PeterMunirAzmy/Automated-Production-line/Mechatronics System Desigen/RobotArm_mechanical_design/files/GearRotate_-0.10mmTolerance.stl

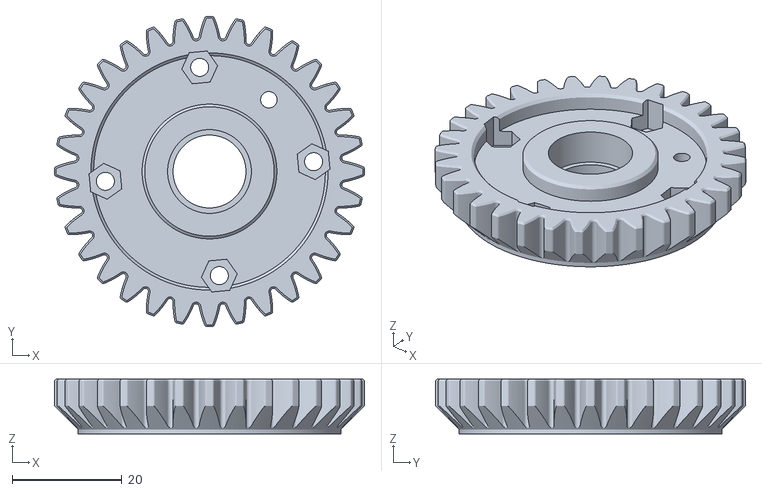
[picture p67: CAD file, 2024-07-03]
Mechatronics System Desigen/RobotArm_mechanical_design/files/GearRotate_-0.10mmTolerance.stl
56.6 x 56.6 x 10.0
