PeterMunirAzmy/Automated-Production-line/Mechatronics System Desigen/Feeding_mechanical_design/feeding_stepper_stand.stp

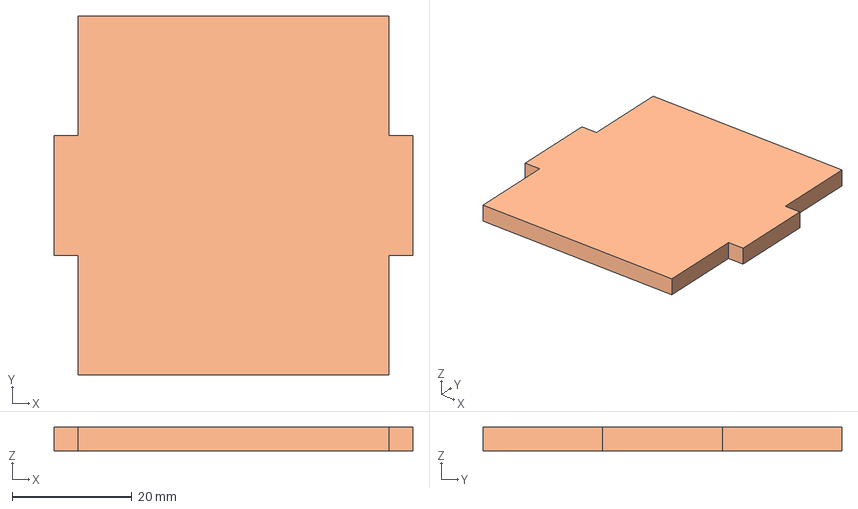
[picture p68: CAD file, 2024-07-03]
Mechatronics System Desigen/Feeding_mechanical_design/feeding_stepper_stand.stp
60.0 x 60.0 x 4.00 mm
