PeterMunirAzmy/Automated-Production-line/Mechatronics System Desigen/Robot_Arm_simulation_on_Matlab/ForwardKinematics/base_w_hole_ipt_7cfa0195.STEP

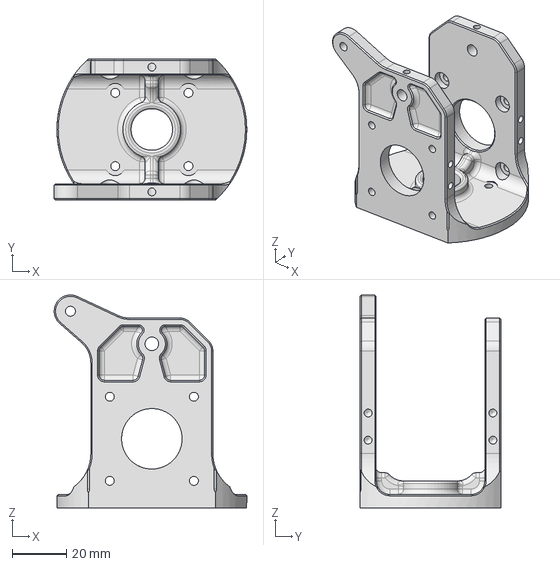
[picture p69: CAD file, 2024-07-03]
Mechatronics System Desigen/Robot_Arm_simulation_on_Matlab/ForwardKinematics/base_w_hole_ipt_7cfa0195.STEP
71.0 x 52.0 x 78.5 mm
