PeterMunirAzmy/Automated-Production-line/Mechatronics System Desigen/Robot_Arm_simulation_on_Matlab/trajectory/GearBig_0.20mmTolerance_ipt_e1a5b1e9.STEP

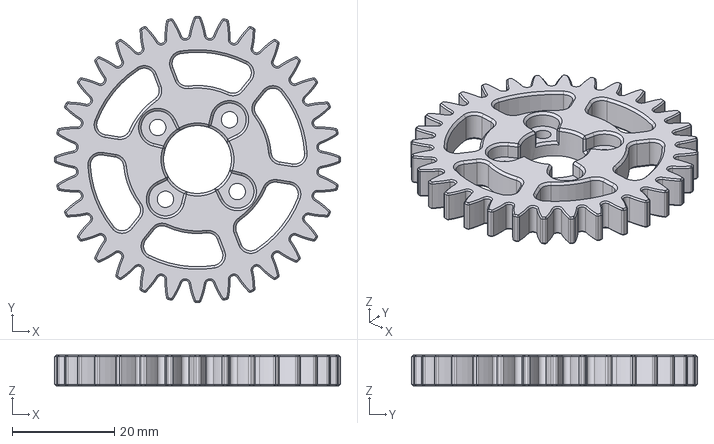
[picture p70: CAD file, 2024-07-03]
Mechatronics System Desigen/Robot_Arm_simulation_on_Matlab/trajectory/GearBig_0.20mmTolerance_ipt_e1a5b1e9.STEP
56.0 x 56.0 x 6.00 mm
