PeterMunirAzmy/Automated-Production-line/Mechatronics System Desigen/Feeding_mechanical_design/feeding_rotating_plate.stp

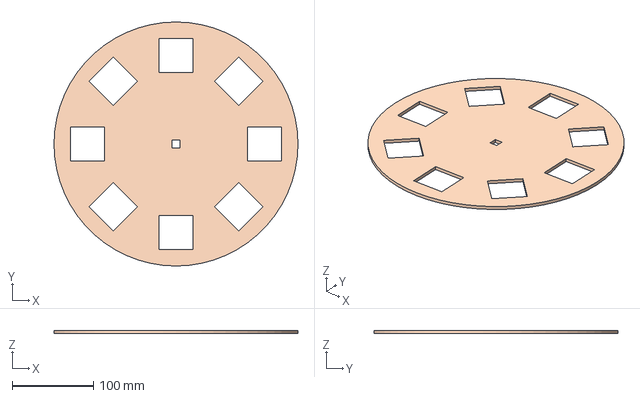
[picture p71: CAD file, 2024-07-03]
Mechatronics System Desigen/Feeding_mechanical_design/feeding_rotating_plate.stp
300.0 x 300.0 x 4.00 mm
