PeterMunirAzmy/Automated-Production-line/Mechatronics System Desigen/RobotArm_mechanical_design/files/gripperBase.stl

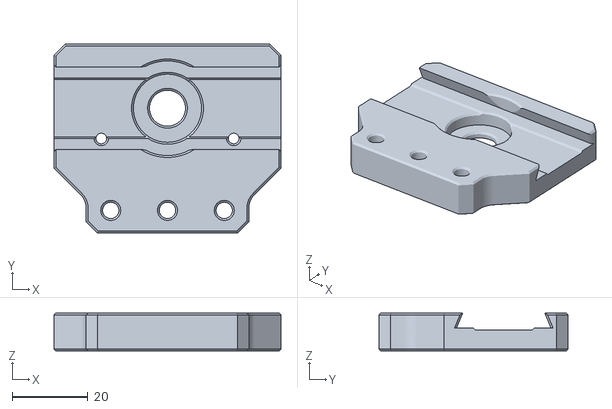
[picture p72: CAD file, 2024-07-03]
Mechatronics System Desigen/RobotArm_mechanical_design/files/gripperBase.stl
60.0 x 50.0 x 10.0
