PeterMunirAzmy/Automated-Production-line/Mechatronics System Desigen/Feeding_mechanical_design/stepper.stp

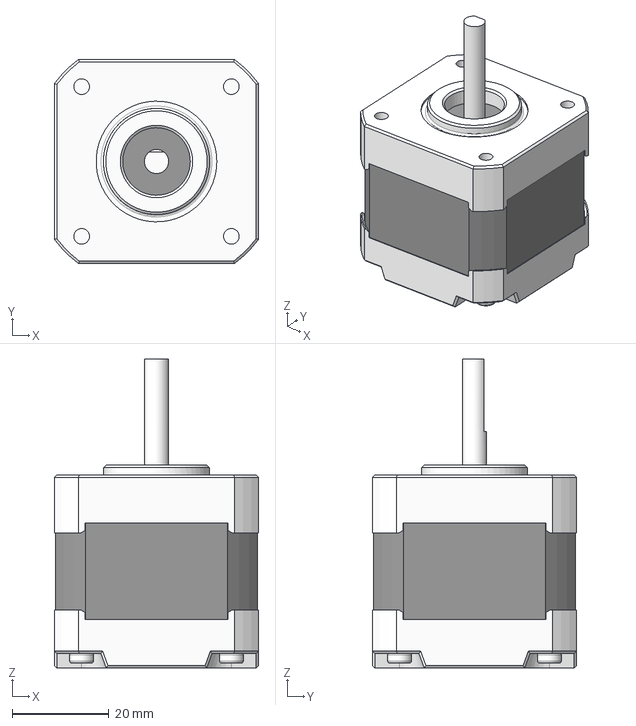
[picture p73: CAD file, 2024-07-03]
Mechatronics System Desigen/Feeding_mechanical_design/stepper.stp
42.3 x 42.3 x 64.0 mm
