PeterMunirAzmy/Automated-Production-line/Mechatronics System Desigen/Feeding_mechanical_design/feeding_stepper_side.stp

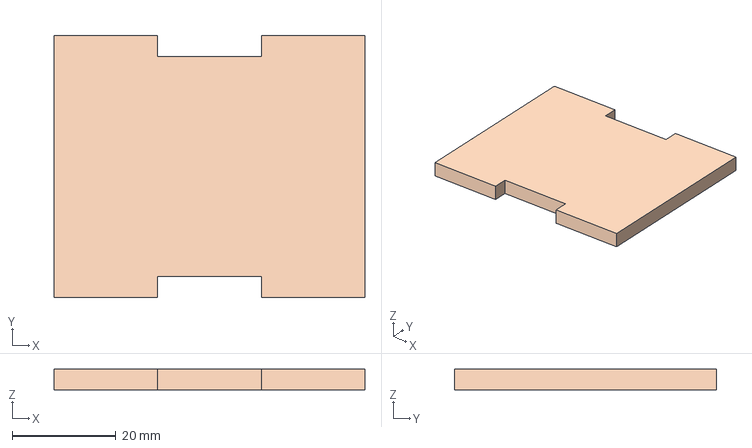
[picture p74: CAD file, 2024-07-03]
Mechatronics System Desigen/Feeding_mechanical_design/feeding_stepper_side.stp
60.0 x 50.5 x 4.00 mm
