PeterMunirAzmy/Automated-Production-line/Mechatronics System Desigen/RobotArm_mechanical_design/files/pleuel_bend.stl

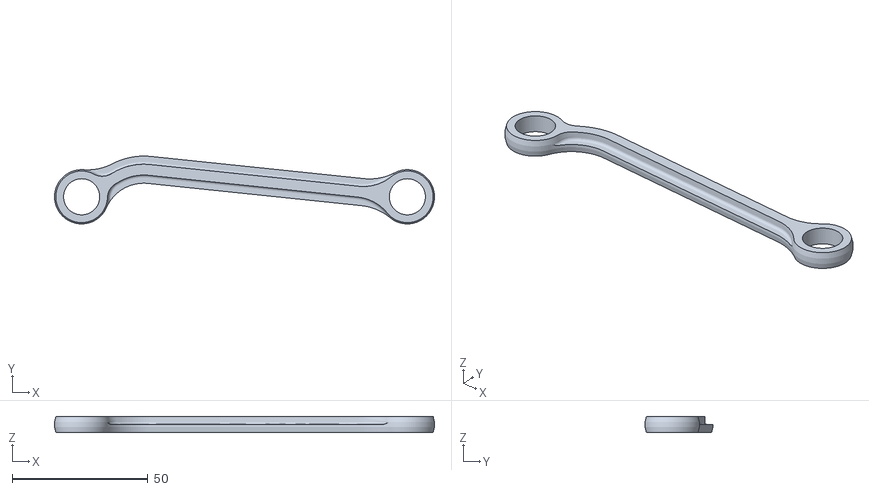
[picture p75: CAD file, 2024-07-03]
Mechatronics System Desigen/RobotArm_mechanical_design/files/pleuel_bend.stl
140.0 x 25.0 x 6.00
