PeterMunirAzmy/Automated-Production-line/Mechatronics System Desigen/RobotArm_mechanical_design/files/gripperHolePlate.stl

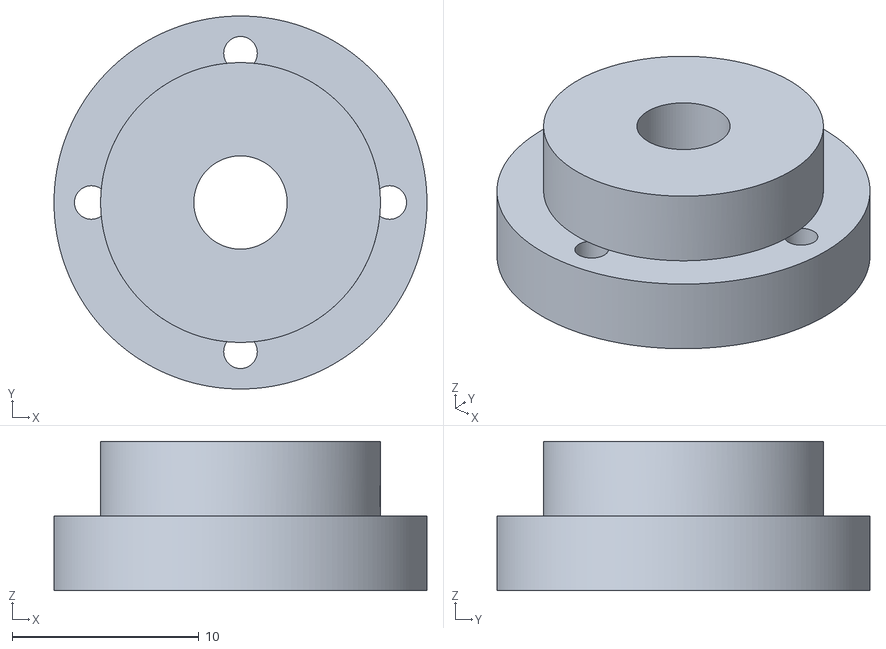
[picture p76: CAD file, 2024-07-03]
Mechatronics System Desigen/RobotArm_mechanical_design/files/gripperHolePlate.stl
20.0 x 20.0 x 8.00
