PeterMunirAzmy/Automated-Production-line/Mechatronics System Desigen/RobotArm_mechanical_design/files/stabilizer.stl

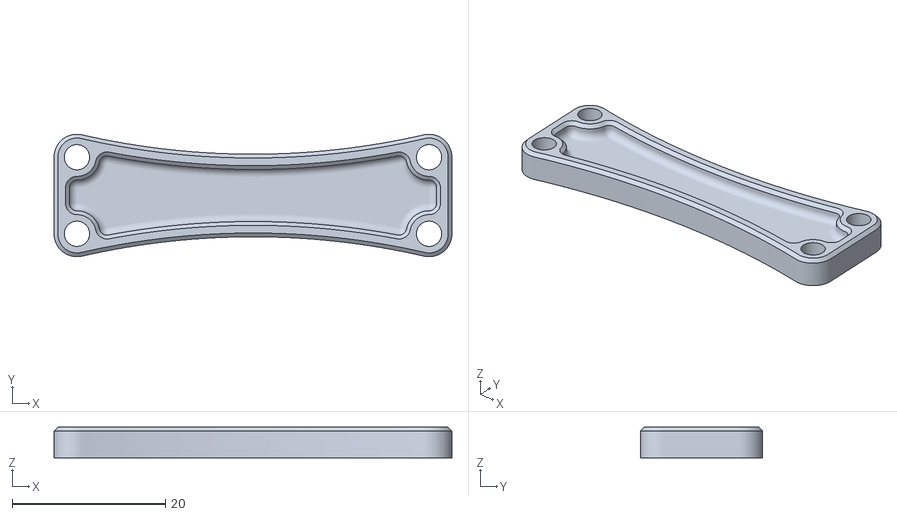
[picture p77: CAD file, 2024-07-03]
Mechatronics System Desigen/RobotArm_mechanical_design/files/stabilizer.stl
52.0 x 16.0 x 4.00
