PeterMunirAzmy/Automated-Production-line/Mechatronics System Desigen/RobotArm_mechanical_design/files/leg_45mm.stl

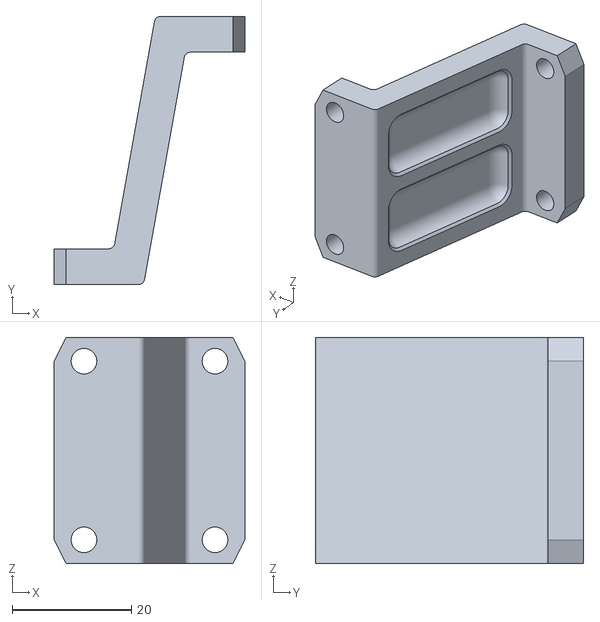
[picture p78: CAD file, 2024-07-03]
Mechatronics System Desigen/RobotArm_mechanical_design/files/leg_45mm.stl
32.0 x 45.0 x 38.0
