PeterMunirAzmy/Automated-Production-line/Mechatronics System Desigen/RobotArm_mechanical_design/files/pleuel.stl

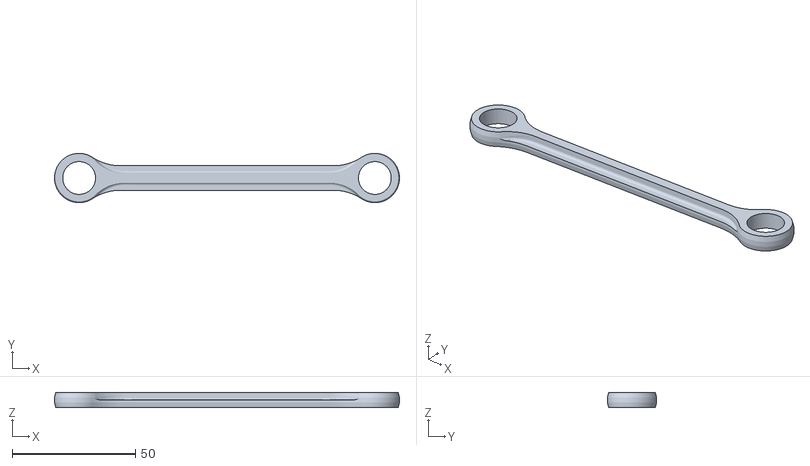
[picture p79: CAD file, 2024-07-03]
Mechatronics System Desigen/RobotArm_mechanical_design/files/pleuel.stl
140.0 x 20.0 x 6.00
