PeterMunirAzmy/Automated-Production-line/Mechatronics System Desigen/RobotArm_mechanical_design/files/GearBig_0.01mmTolerance.stl

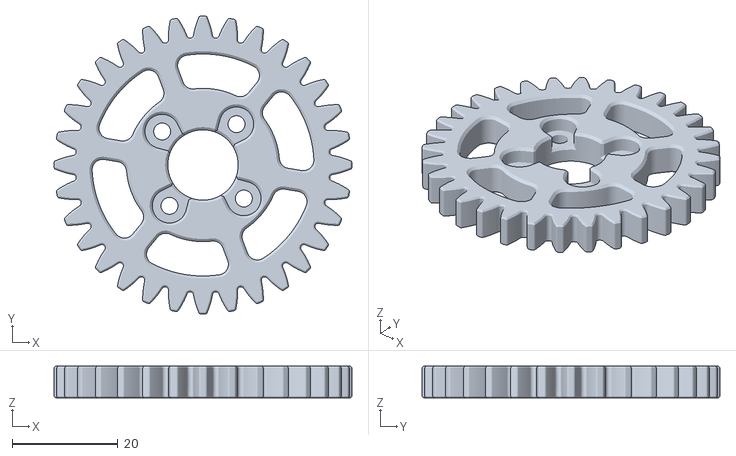
[picture p80: CAD file, 2024-07-03]
Mechatronics System Desigen/RobotArm_mechanical_design/files/GearBig_0.01mmTolerance.stl
56.4 x 56.4 x 6.00
