PeterMunirAzmy/Automated-Production-line/Mechatronics System Desigen/RobotArm_mechanical_design/files/triplate.stl

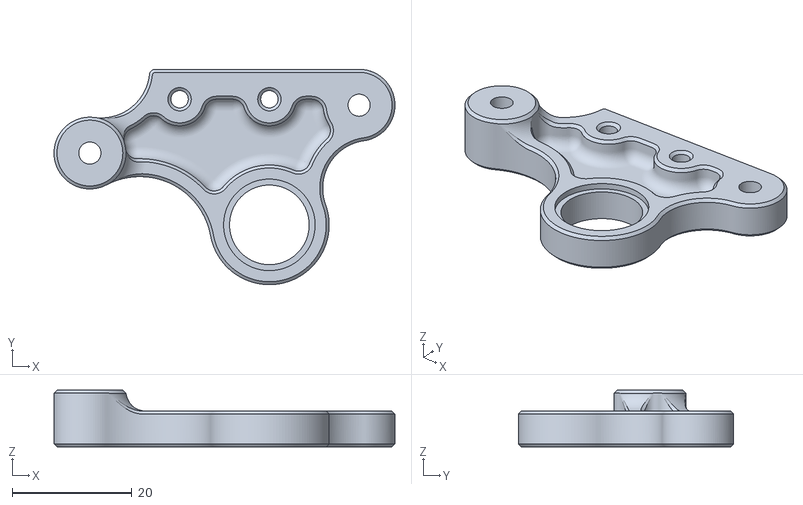
[picture p81: CAD file, 2024-07-03]
Mechatronics System Desigen/RobotArm_mechanical_design/files/triplate.stl
57.0 x 36.0 x 9.50
