PeterMunirAzmy/Automated-Production-line/Mechatronics System Desigen/RobotArm_mechanical_design/files/lever.stl

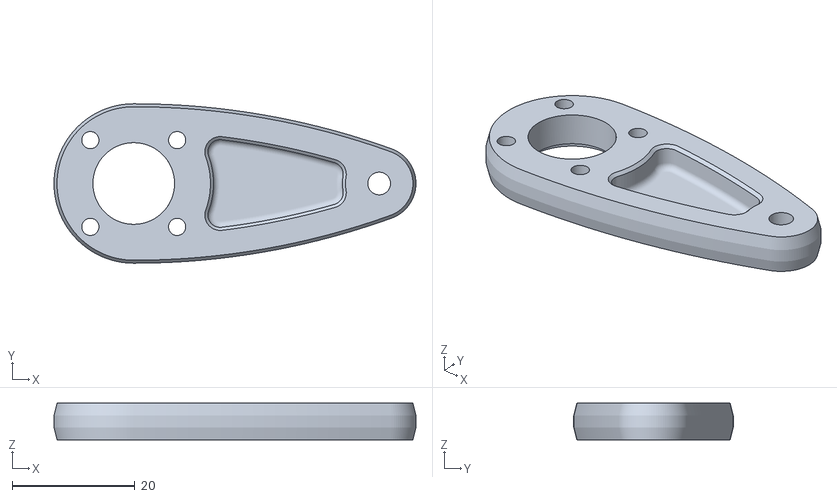
[picture p82: CAD file, 2024-07-03]
Mechatronics System Desigen/RobotArm_mechanical_design/files/lever.stl
59.0 x 26.0 x 6.00
