PeterMunirAzmy/Automated-Production-line/Mechatronics System Desigen/RobotArm_mechanical_design/files/leg_35mm.stl

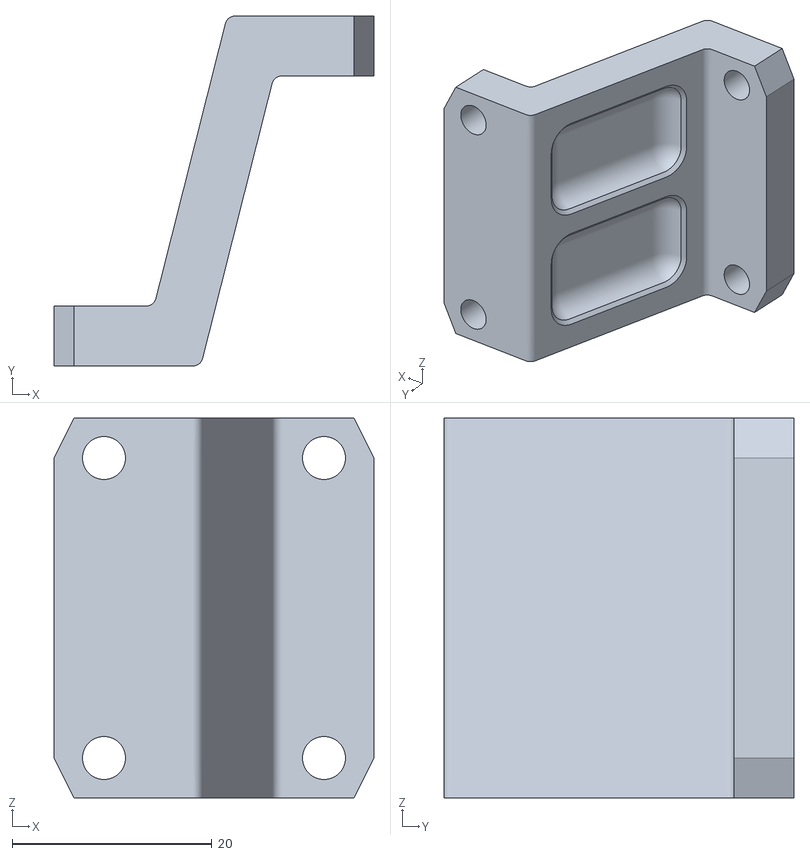
[picture p83: CAD file, 2024-07-03]
Mechatronics System Desigen/RobotArm_mechanical_design/files/leg_35mm.stl
32.0 x 35.0 x 38.0
