PeterMunirAzmy/Automated-Production-line/Mechatronics System Desigen/RobotArm_mechanical_design/files/leg_50mm.stl

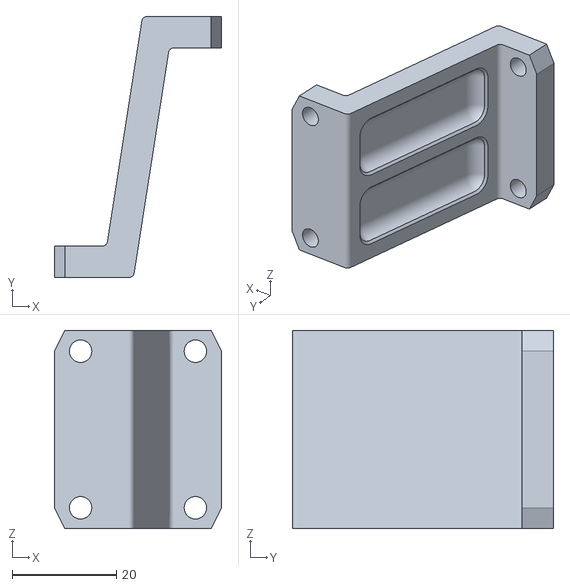
[picture p84: CAD file, 2024-07-03]
Mechatronics System Desigen/RobotArm_mechanical_design/files/leg_50mm.stl
32.0 x 50.0 x 38.0
