PeterMunirAzmy/Automated-Production-line/Mechatronics System Desigen/RobotArm_mechanical_design/files/manipulator.stl

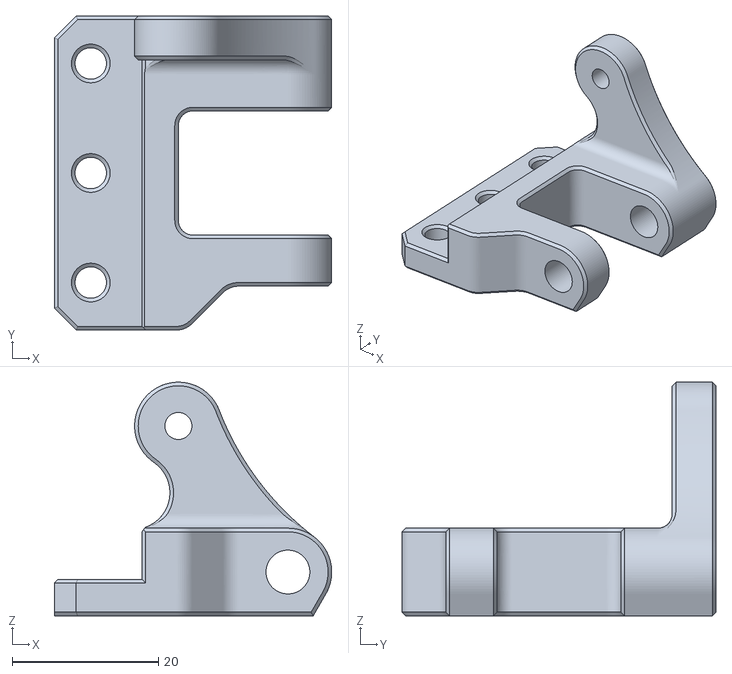
[picture p85: CAD file, 2024-07-03]
Mechatronics System Desigen/RobotArm_mechanical_design/files/manipulator.stl
38.0 x 43.0 x 32.0
