PeterMunirAzmy/Automated-Production-line/Mechatronics System Desigen/RobotArm_mechanical_design/files/leg_40mm.stl

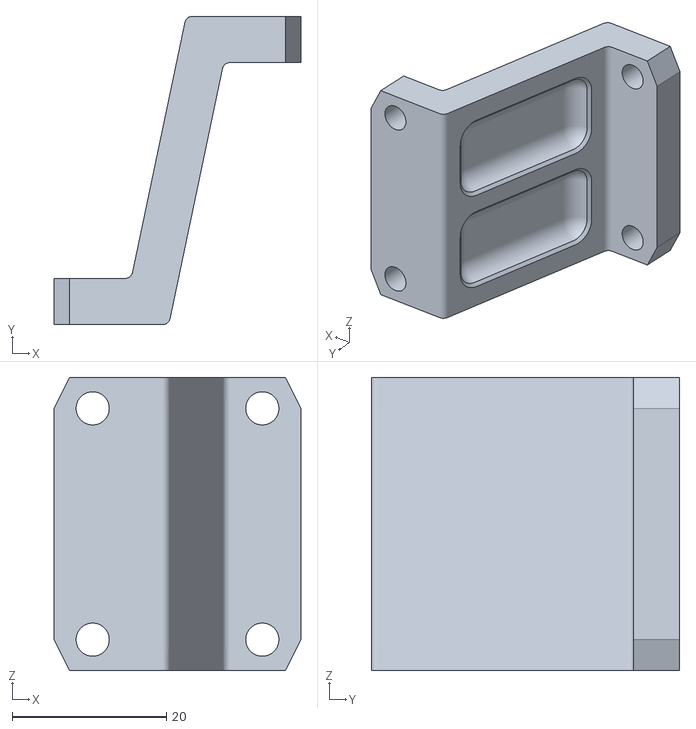
[picture p86: CAD file, 2024-07-03]
Mechatronics System Desigen/RobotArm_mechanical_design/files/leg_40mm.stl
32.0 x 40.0 x 38.0
