PeterMunirAzmy/Automated-Production-line/Mechatronics System Desigen/RobotArm_mechanical_design/files/GearSmall.stl

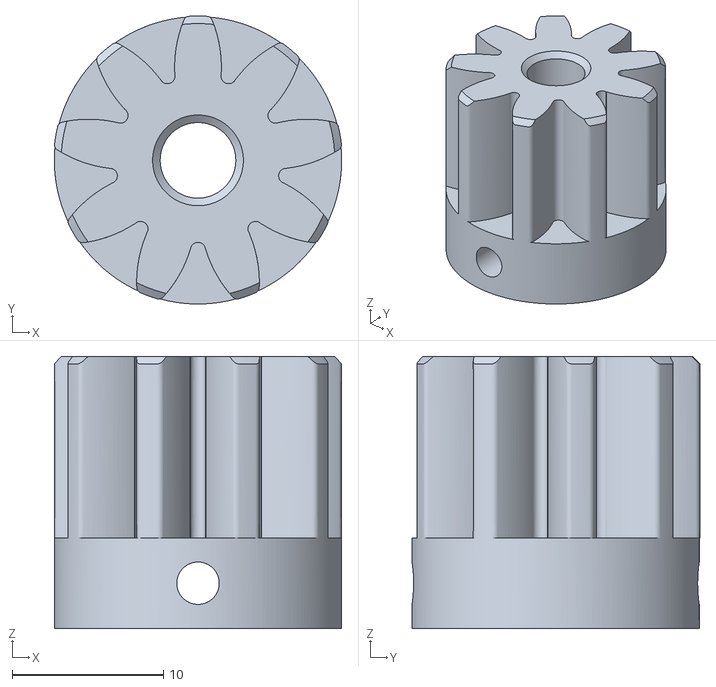
[picture p87: CAD file, 2024-07-03]
Mechatronics System Desigen/RobotArm_mechanical_design/files/GearSmall.stl
19.0 x 19.0 x 18.0
