PeterMunirAzmy/Automated-Production-line/Mechatronics System Desigen/RobotArm_mechanical_design/files/stabilizer_endstop.stl

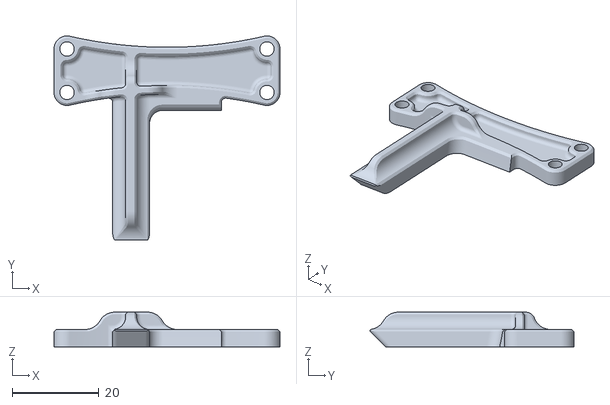
[picture p88: CAD file, 2024-07-03]
Mechatronics System Desigen/RobotArm_mechanical_design/files/stabilizer_endstop.stl
52.0 x 47.0 x 8.00
