PeterMunirAzmy/Automated-Production-line/Mechatronics System Desigen/RobotArm_mechanical_design/files/control_bottom.stl

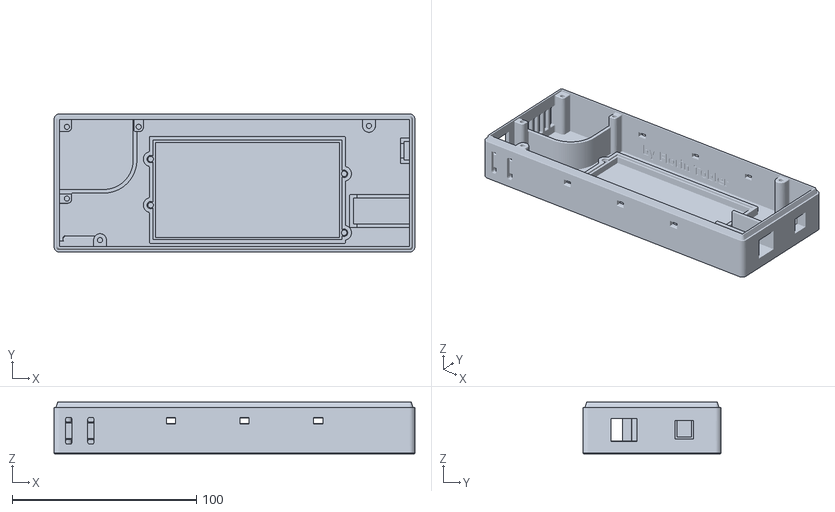
[picture p89: CAD file, 2024-07-03]
Mechatronics System Desigen/RobotArm_mechanical_design/files/control_bottom.stl
196.0 x 75.0 x 28.0
