PeterMunirAzmy/Automated-Production-line/Mechatronics System Desigen/Code/pythonProject/TestImg/objects3.jpg

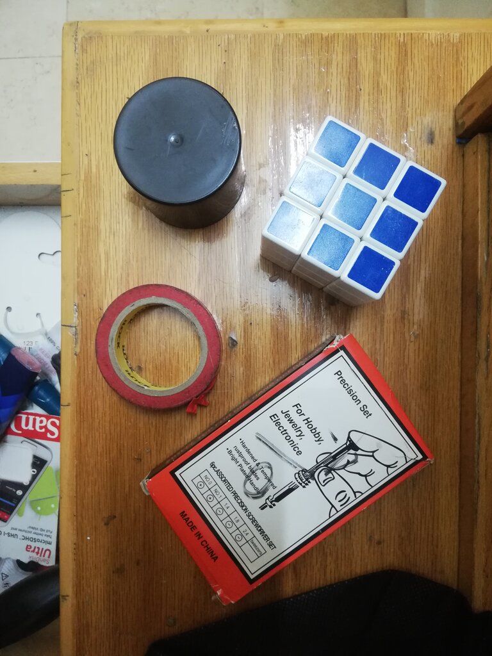
Mechatronics System Desigen/Code/pythonProject/TestImg/objects3.jpg
