PeterMunirAzmy/Automated-Production-line/Mechatronics System Desigen/Code/pythonProject/TestImg/objects7 (1).jpg

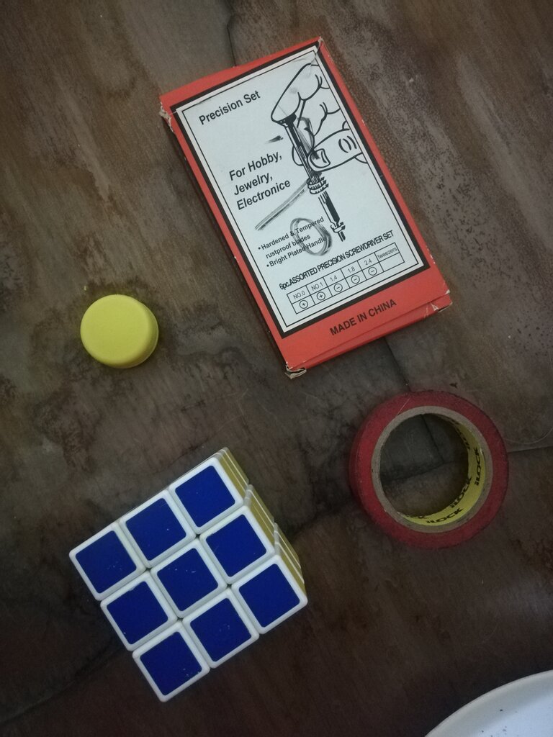
Mechatronics System Desigen/Code/pythonProject/TestImg/objects7 (1).jpg
